akouz/HBnode/AVR64DD32/Bootloader/flash_access.h

/**
 * \file flash_access.h
 *
 * \brief Flash access functions.
 *
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
 */

#ifndef FLASH_ACCESS_H_
#define FLASH_ACCESS_H_

#ifdef __cplusplus
extern "C" {
#endif
    
// Read program memory byte from specified address 
extern uint8_t pgm_byte_read(uint16_t addrr);

// Write a word in program memory at a specific address
extern void pgm_word_write(uint16_t addrr, uint16_t data);

#ifdef __cplusplus
}
#endif

#endif /* FLASH_ACCESS_H_ */
